jesyblue/EVA-mod-for-load-cel-probe/firmware/connections.jpg

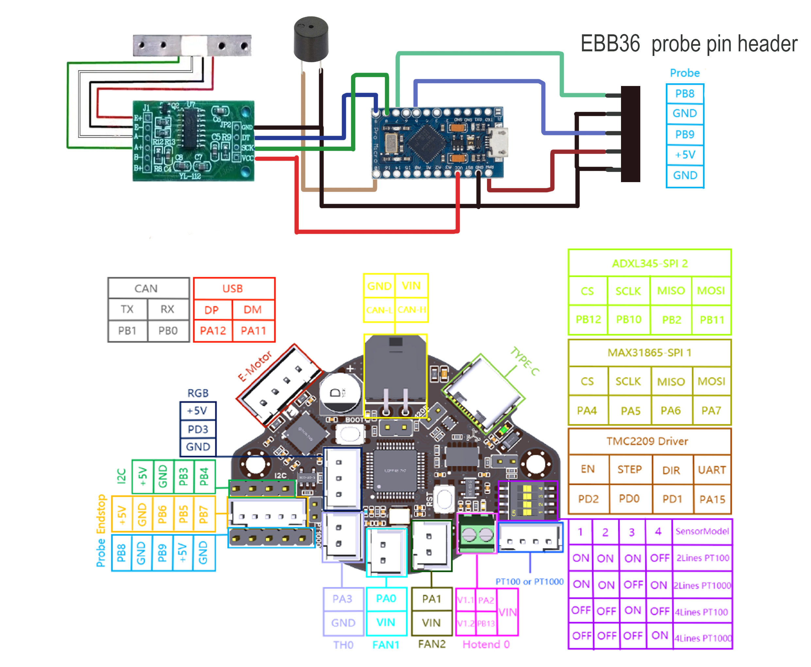
firmware/connections.jpg
