jesyblue/EVA-mod-for-load-cel-probe/img/cell_cut_1.jpg

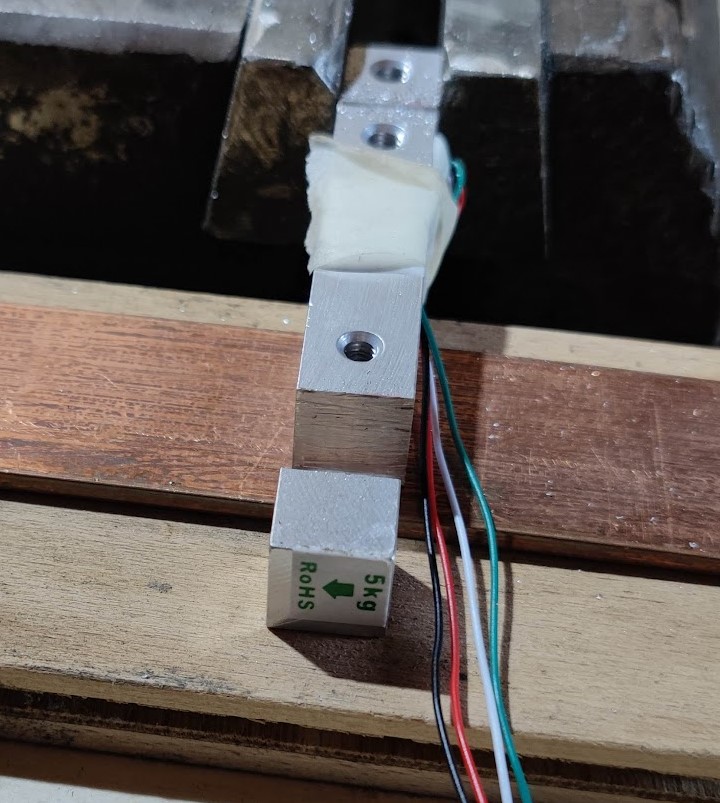
img/cell_cut_1.jpg
