jesyblue/EVA-mod-for-load-cel-probe/img/cell_cut_2.jpg

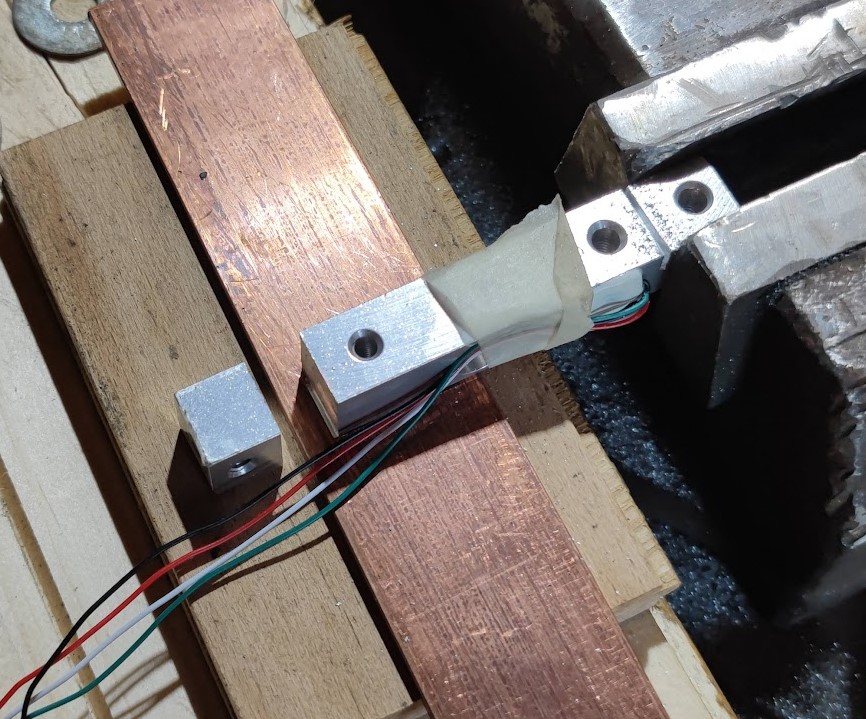
img/cell_cut_2.jpg
