jesyblue/EVA-mod-for-load-cel-probe/img/cell_mount_1.jpg

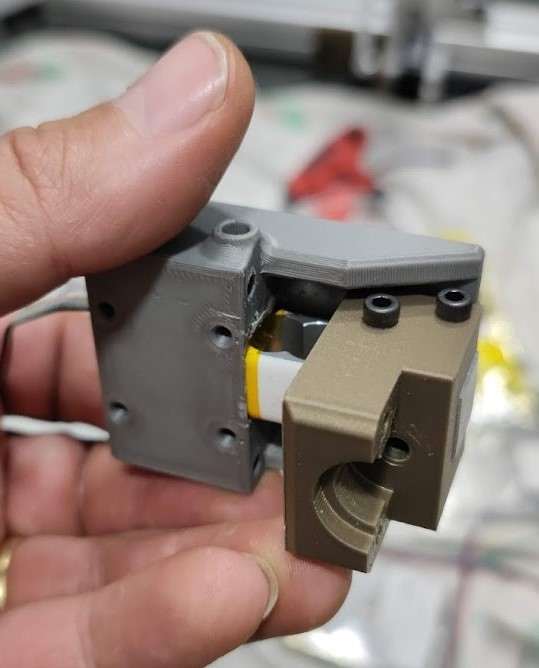
img/cell_mount_1.jpg
