jesyblue/EVA-mod-for-load-cel-probe/img/cell_mount_2.jpg

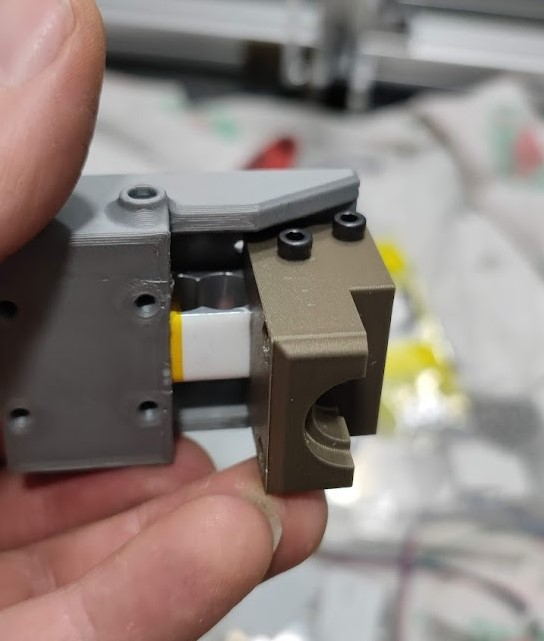
img/cell_mount_2.jpg
