jesyblue/EVA-mod-for-load-cel-probe/img/cell_mount_3.jpg

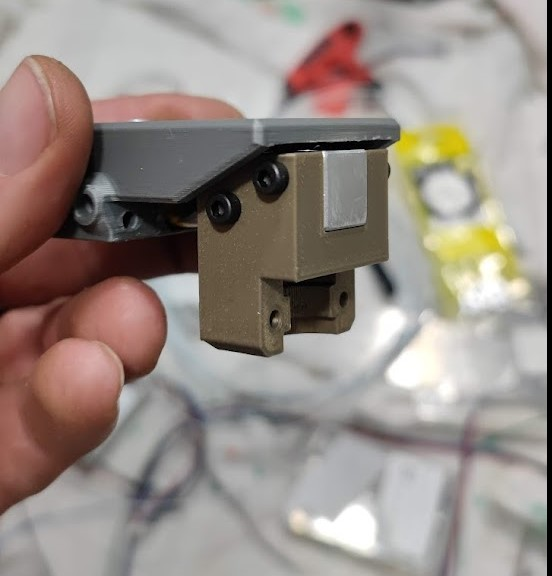
img/cell_mount_3.jpg
