jesyblue/EVA-mod-for-load-cel-probe/img/electronnics_head.jpg

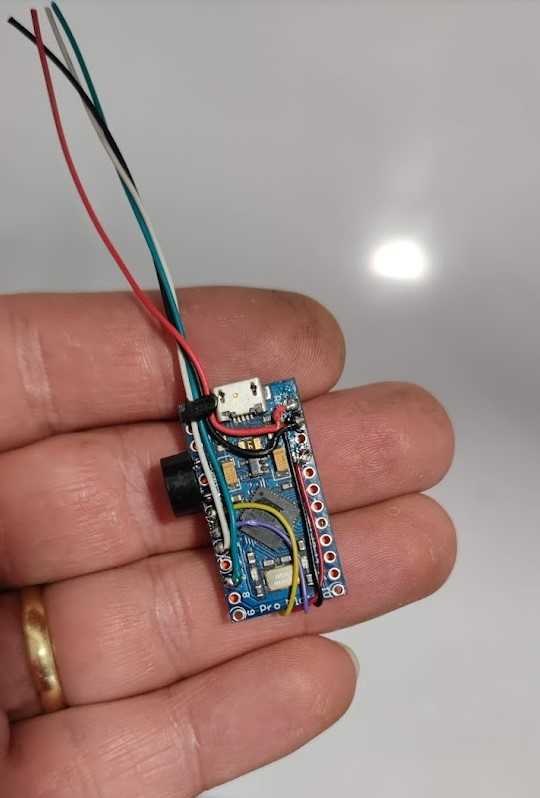
img/electronnics_head.jpg
