jesyblue/EVA-mod-for-load-cel-probe/img/electronnics_head_1.jpg

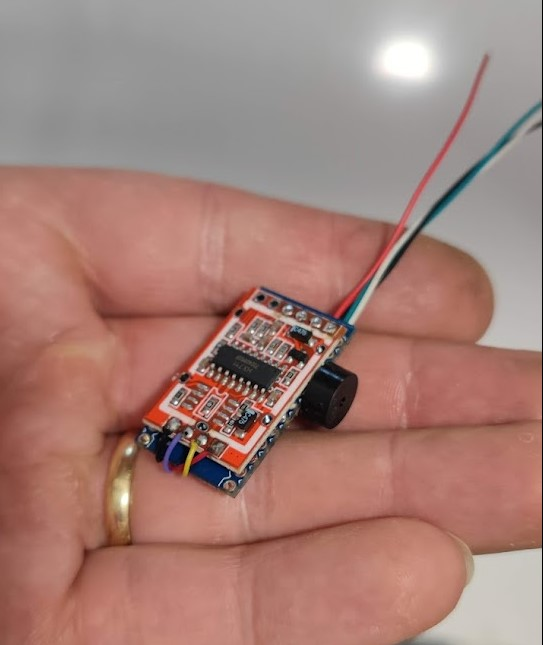
img/electronnics_head_1.jpg
