jesyblue/EVA-mod-for-load-cel-probe/img/preview7.png

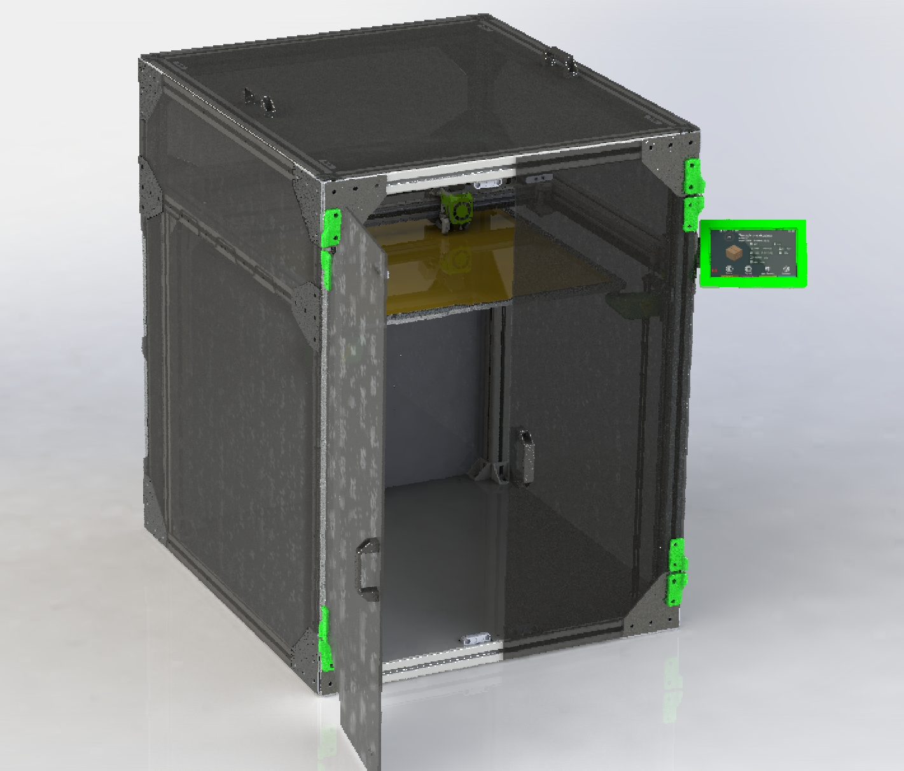
img/preview7.png
