jesyblue/EVA-mod-for-load-cel-probe/img/toolhead_1.jpg

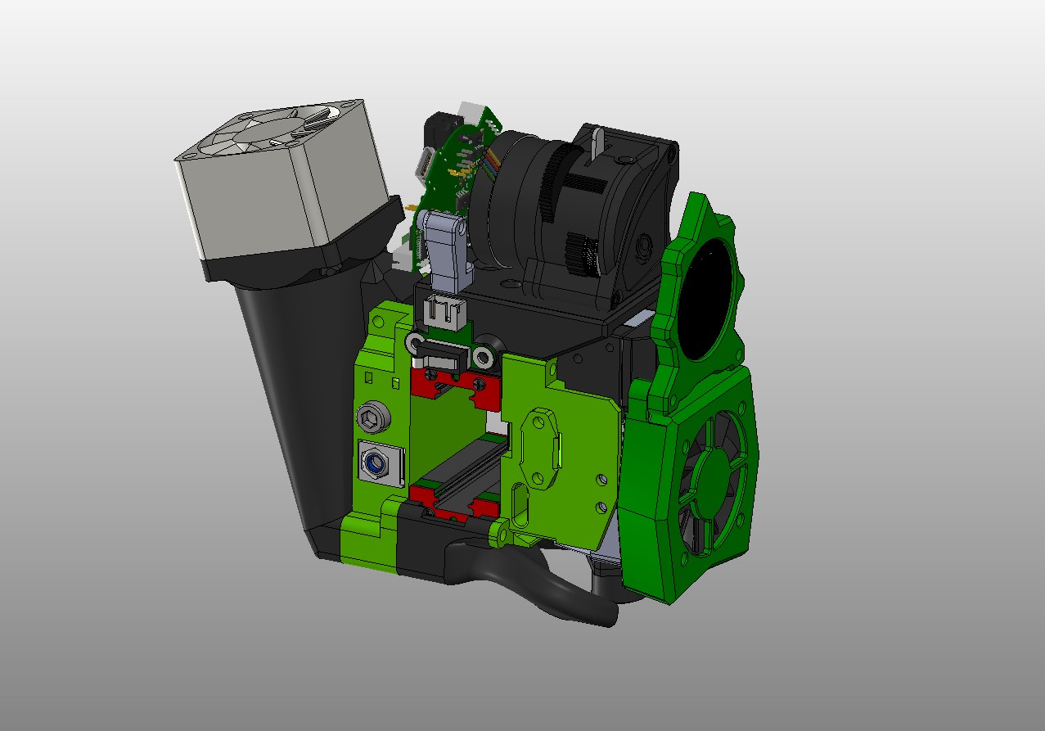
img/toolhead_1.jpg
