jesyblue/EVA-mod-for-load-cel-probe/img/toolhead_3.jpg

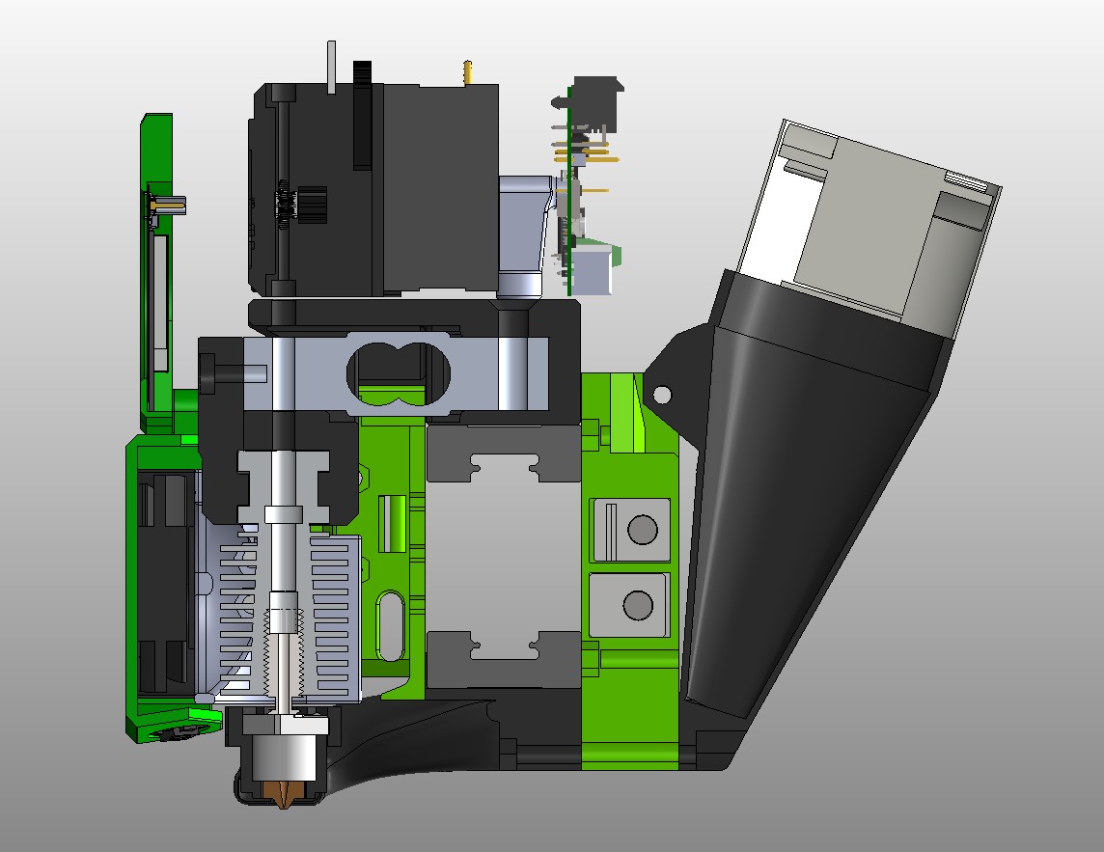
img/toolhead_3.jpg
