jesyblue/EVA-mod-for-load-cel-probe/img/toolhead_4.jpg

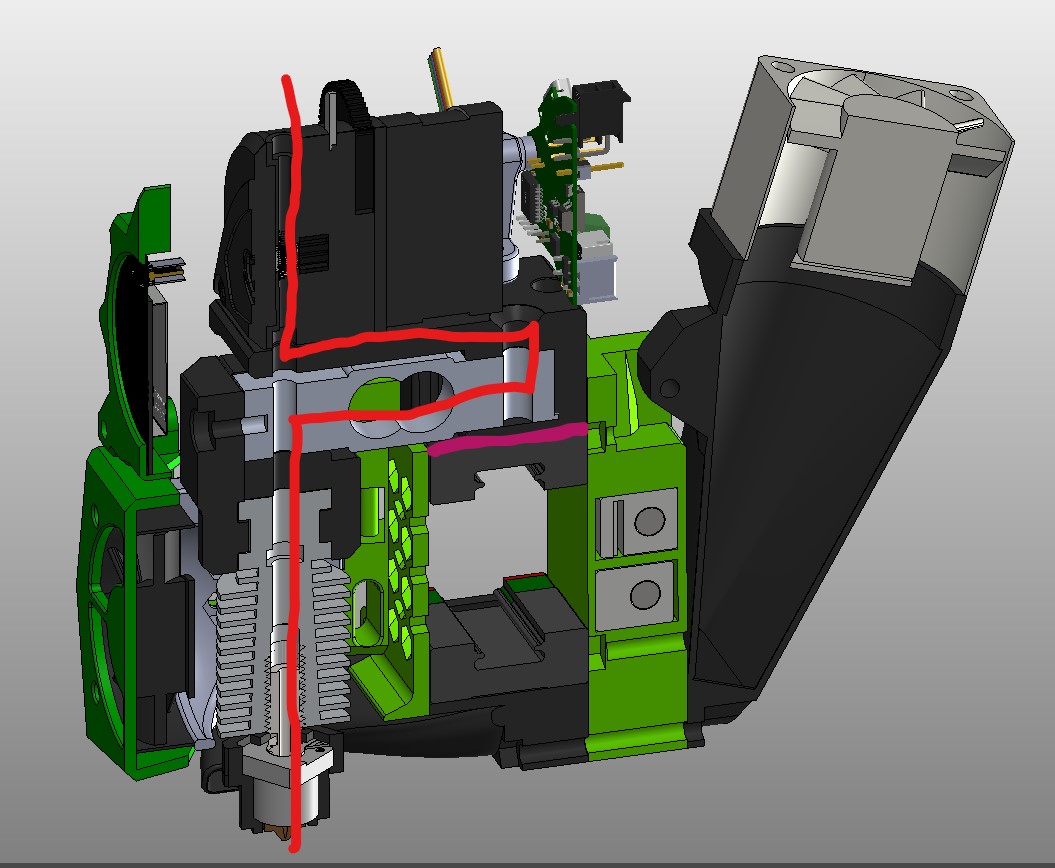
img/toolhead_4.jpg
