jesyblue/EVA-mod-for-load-cel-probe/img/toolhead_6.jpg

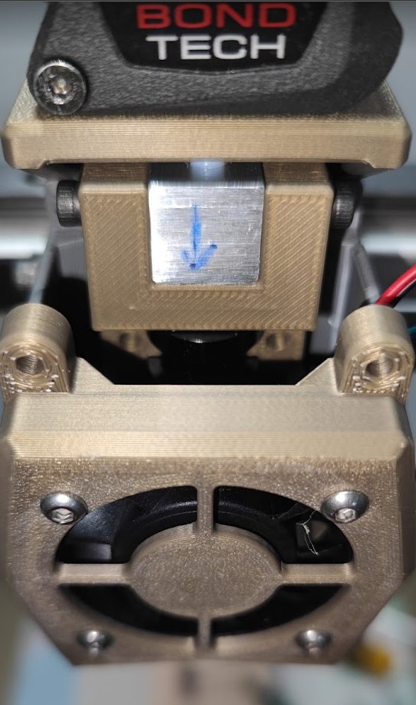
img/toolhead_6.jpg
